JohnanLuca02/BYTE_Electronics/Good_Boy_Limiter/SPICE/LM5069_SPICE.asc

C1: cap; 1µ
C2: cap; 220µ
C3: cap; 8m
D1: diode
M1: nmos
R1: res; 150k
R2: res; 20m
R3: res; 10k
U1: LM5069-2_TRANS
V1: voltage; 48V
V2: voltage; 60V
V3: voltage; 20V
V4: voltage; 3.3
Named nets: 0, Vin, Vout, 60V, 20V, VDD, GPIO, Vsns
